rappepi/ESP32-S3-keyboard/hardware/Clavier.kicad_sch

## KiCad design hardware/Clavier.kicad_sch (2025-09-21)

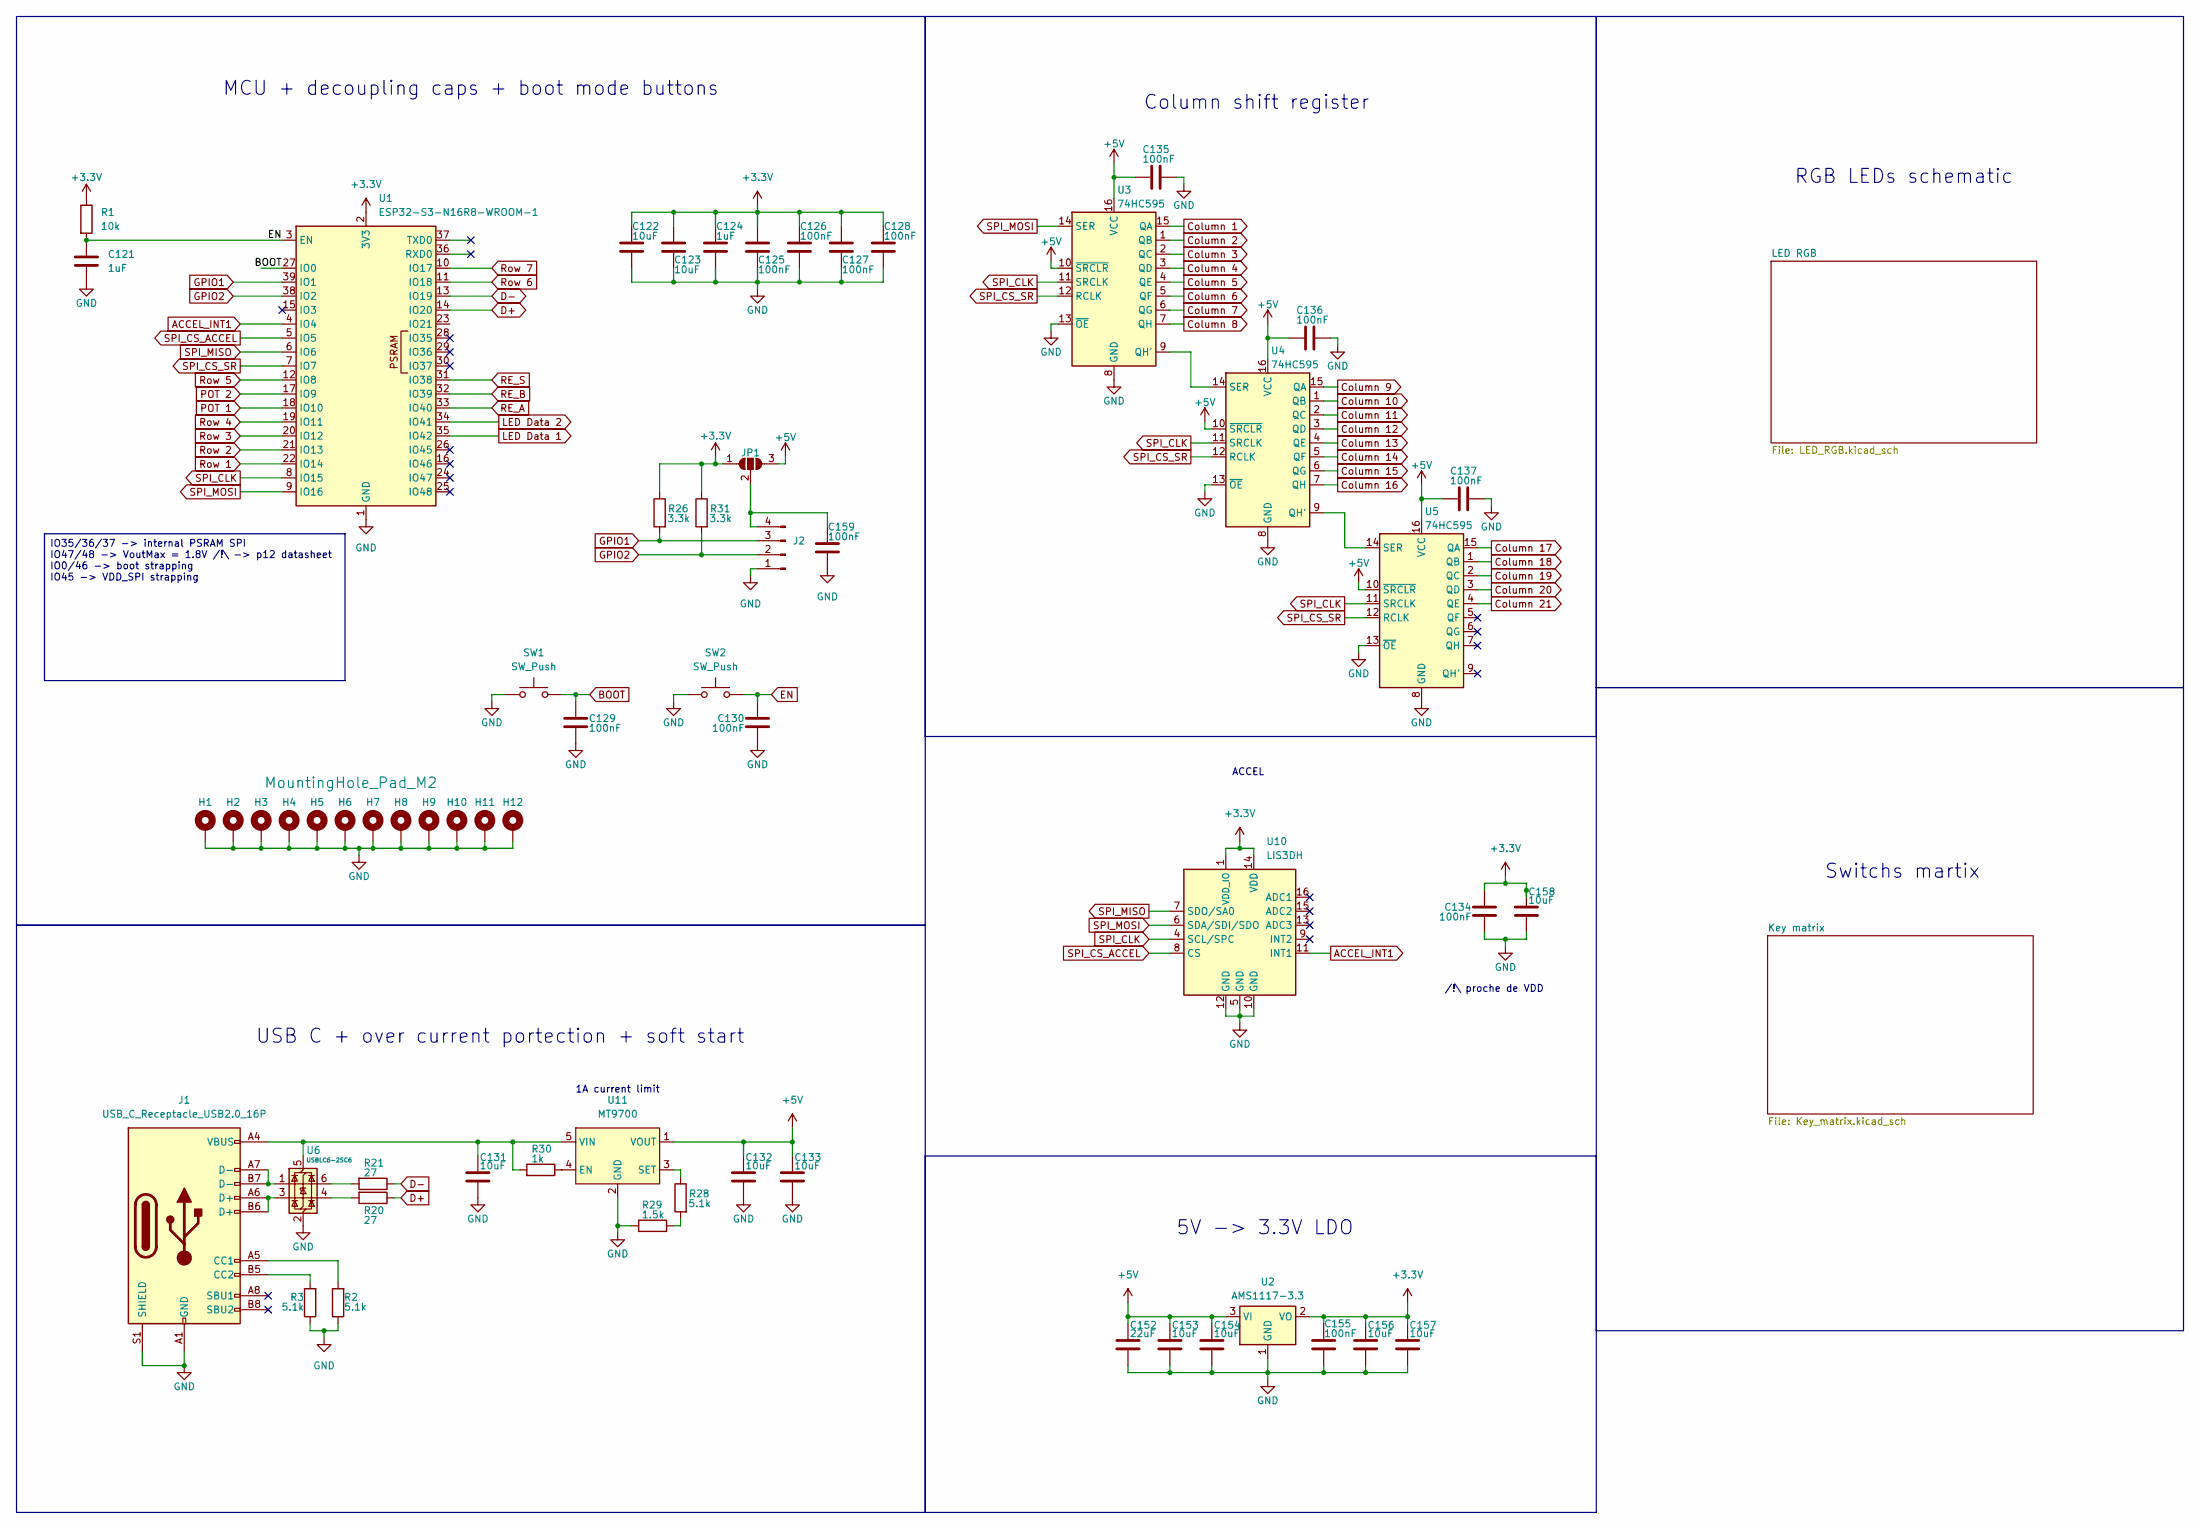
[picture p8: schematic Clavier.kicad_sch]

Parts:
C121, C124: 1uF; C_0402_1005Metric_Pad0.74x0.62mm_HandSolder
C122, C123: 10uF; C_0402_1005Metric_Pad0.74x0.62mm_HandSolder
C125, C126, C127, C128, C129, C130, C134, C135, C136, C137, C155, C159: 100nF; C_0402_1005Metric_Pad0.74x0.62mm_HandSolder
C131, C132, C133, C153, C154, C156, C157, C158: 10uF; C_0603_1608Metric_Pad1.08x0.95mm_HandSolder
C152: 22uF; C_1206_3216Metric_Pad1.33x1.80mm_HandSolder
H1, H2, H3, H4, H5, H6, H7, H8, H9, H10, H11, H12: MountingHole_Pad_M2; MountingHole_2.2mm_M2_ISO7380_Pad
J1: USB_C_Receptacle_USB2.0_16P; USB_C_Receptacle_G-Switch_GT-USB-7010ASV
J2: Conn_01x04_Pin; PinHeader_1x04_P2.54mm_Vertical
JP1: SolderJumper_3_Open; SolderJumper-3_P1.3mm_Open_Pad1.0x1.5mm_NumberLabels
R1: 10k; R_0402_1005Metric_Pad0.72x0.64mm_HandSolder
R2, R3, R28: 5.1k; R_0603_1608Metric_Pad0.98x0.95mm_HandSolder
R20, R21: 27; R_0603_1608Metric_Pad0.98x0.95mm_HandSolder
R26, R31: 3.3k; R_0603_1608Metric_Pad0.98x0.95mm_HandSolder
R29: 1.5k; R_0603_1608Metric_Pad0.98x0.95mm_HandSolder
R30: 1k; R_0603_1608Metric_Pad0.98x0.95mm_HandSolder
SW1, SW2: SW_Push; SW_SPST_SKQG_WithoutStem
U1: ESP32-S3-N16R8-WROOM-1; ESP32-S3-WROOM-1
U2: AMS1117-3.3; SOT-223-3_TabPin2
U3, U4, U5: 74HC595; SOP-16_3.9x9.9mm_P1.27mm
U6: USBLC6-2SC6; SOT-23-6
U10: LIS3DH; LGA-16_3x3mm_P0.5mm_LayoutBorder3x5y
U11: MT9700; SOT-23-5_L3.0-W1.7-P0.95-LS2.8-BR; LCSC Part C89855

Connections:
+3.3V: C122.1, C123.1, C124.1, C125.1, C126.1, C127.1, C128.1, C134.1, C155.1, C156.1, C157.1, C158.1, JP1.1 (A), R1.1, R26.1, R31.1, U1.2 (3V3), U2.2 (VO), U10.1 (VDD_IO), U10.14 (VDD)
+5V: C132.1, C133.1, C135.2, C136.2, C137.2, C152.1, C153.1, C154.1, JP1.3 (B), U2.3 (VI), U3.10 (~SRCLR), U3.16 (VCC), U4.10 (~SRCLR), U4.16 (VCC), U5.10 (~SRCLR), U5.16 (VCC), U11.1 (VOUT)
ACCEL_INT1: U1.4 (IO4), U10.11 (INT1)
BOOT: C129.1, SW1.2, U1.27 (IO0)
Column 1: U3.15 (QA)
Column 2: U3.1 (QB)
Column 3: U3.2 (QC)
Column 4: U3.3 (QD)
Column 5: U3.4 (QE)
Column 6: U3.5 (QF)
Column 7: U3.6 (QG)
Column 8: U3.7 (QH)
Column 9: U4.15 (QA)
Column 10: U4.1 (QB)
Column 11: U4.2 (QC)
Column 12: U4.3 (QD)
Column 13: U4.4 (QE)
Column 14: U4.5 (QF)
Column 15: U4.6 (QG)
Column 16: U4.7 (QH)
Column 17: U5.15 (QA)
Column 18: U5.1 (QB)
Column 19: U5.2 (QC)
Column 20: U5.3 (QD)
Column 21: U5.4 (QE)
D+: R20.1, U1.14 (IO20)
D-: R21.1, U1.13 (IO19)
EN: C121.1, C130.1, R1.2, SW2.2, U1.3 (EN)
GND: C121.2, C122.2, C123.2, C124.2, C125.2, C126.2, C127.2, C128.2, C129.2, C130.2, C131.2, C132.2, C133.2, C134.2, C135.1, C136.1, C137.1, C152.2, C153.2, C154.2, C155.2, C156.2, C157.2, C158.2, C159.2, H1.1, H2.1, H3.1, H4.1, H5.1, H6.1, H7.1, H8.1, H9.1, H10.1, H11.1, H12.1, J1.A1 (GND), J1.A12 (GND), J1.B1 (GND), J1.B12 (GND), J1.S1 (SHIELD), J2.1, R2.1, R3.1, R29.2, SW1.1, SW2.1, U1.1 (GND), U1.40 (GND), U1.41 (GND), U2.1 (GND), U3.8 (GND), U3.13 (~OE), U4.8 (GND), U4.13 (~OE), U5.8 (GND), U5.13 (~OE), U6.2 (GND), U10.5 (GND), U10.10 (GND), U10.12 (GND), U11.2 (GND)
GPIO1: J2.3, R26.2, U1.39 (IO1)
GPIO2: J2.2, R31.2, U1.38 (IO2)
LED Data 1: U1.35 (IO42)
LED Data 2: U1.34 (IO41)
unnamed: C131.1, J1.A4 (VBUS), J1.A9 (VBUS), J1.B4 (VBUS), J1.B9 (VBUS), R30.2, U6.5 (VBUS), U11.5 (VIN)
unnamed: C159.1, J2.4, JP1.2 (C)
unnamed: J1.A5 (CC1), R2.2
unnamed: J1.A6 (D+), J1.B6 (D+), U6.3 (I/O2)
unnamed: J1.A7 (D-), J1.B7 (D-), U6.1 (I/O1)
unnamed: J1.B5 (CC2), R3.2
unnamed: R20.2, U6.4 (I/O2)
unnamed: R21.2, U6.6 (I/O1)
unnamed: R28.1, U11.3 (SET)
unnamed: R28.2, R29.1
unnamed: R30.1, U11.4 (EN)
unnamed: U3.9 (QH'), U4.14 (SER)
unnamed: U4.9 (QH'), U5.14 (SER)
POT 1: U1.18 (IO10)
POT 2: U1.17 (IO9)
RE_A: U1.33 (IO40)
RE_B: U1.32 (IO39)
RE_S: U1.31 (IO38)
Row 1: U1.22 (IO14)
Row 2: U1.21 (IO13)
Row 3: U1.20 (IO12)
Row 4: U1.19 (IO11)
Row 5: U1.12 (IO8)
Row 6: U1.11 (IO18)
Row 7: U1.10 (IO17)
SPI_CLK: U1.8 (IO15), U3.11 (SRCLK), U4.11 (SRCLK), U5.11 (SRCLK), U10.4 (SCL/SPC)
SPI_CS_ACCEL: U1.5 (IO5), U10.8 (CS)
SPI_CS_SR: U1.7 (IO7), U3.12 (RCLK), U4.12 (RCLK), U5.12 (RCLK)
SPI_MISO: U1.6 (IO6), U10.7 (SDO/SA0)
SPI_MOSI: U1.9 (IO16), U3.14 (SER), U10.6 (SDA/SDI/SDO)

Notes on the sheet:
Column shift register
USB C + over current portection + soft start
5V -> 3.3V LDO
MCU + decoupling caps + boot mode buttons
Switchs martix
1A current limit
ACCEL
/!\ proche de VDD
RGB LEDs schematic
IO35/36/37 -> internal PSRAM SPI IO47/48 -> VoutMax = 1.8V /!\ -> p12 datasheet IO0/46 -> boot strapping IO45 -> VDD_SPI strapping
