rappepi/ESP32-S3-keyboard/hardware/LED_RGB.kicad_sch

## KiCad design hardware/LED_RGB.kicad_sch (2025-09-21)

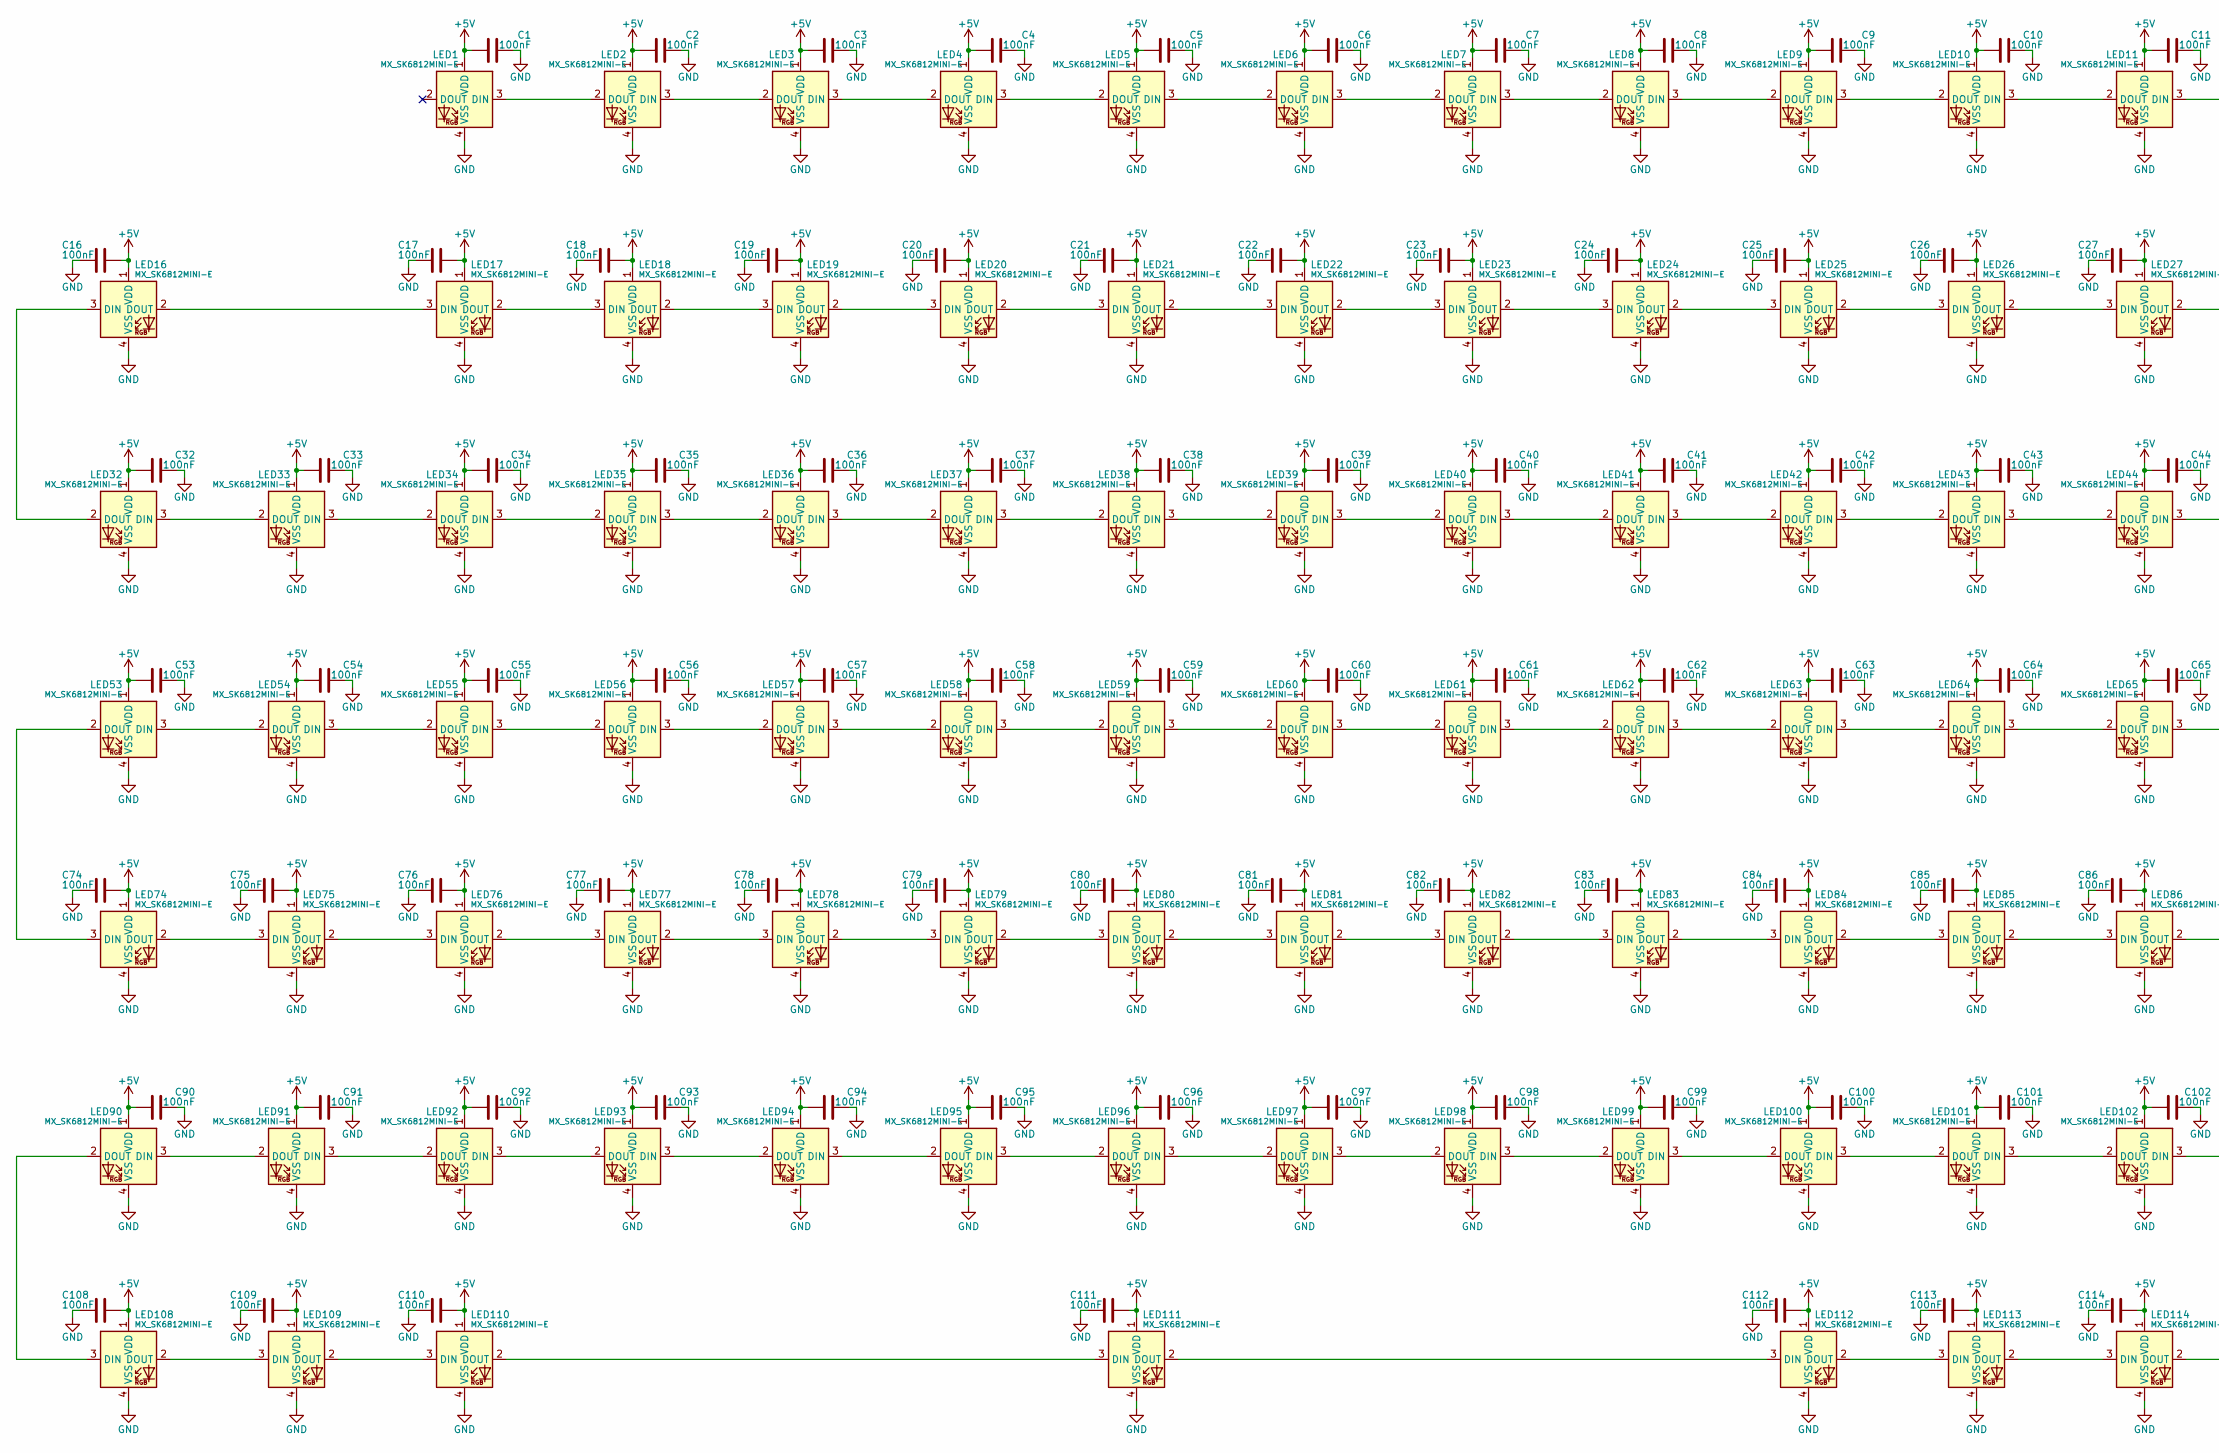
[picture p11: schematic LED_RGB.kicad_sch, part in row 1, column 1]

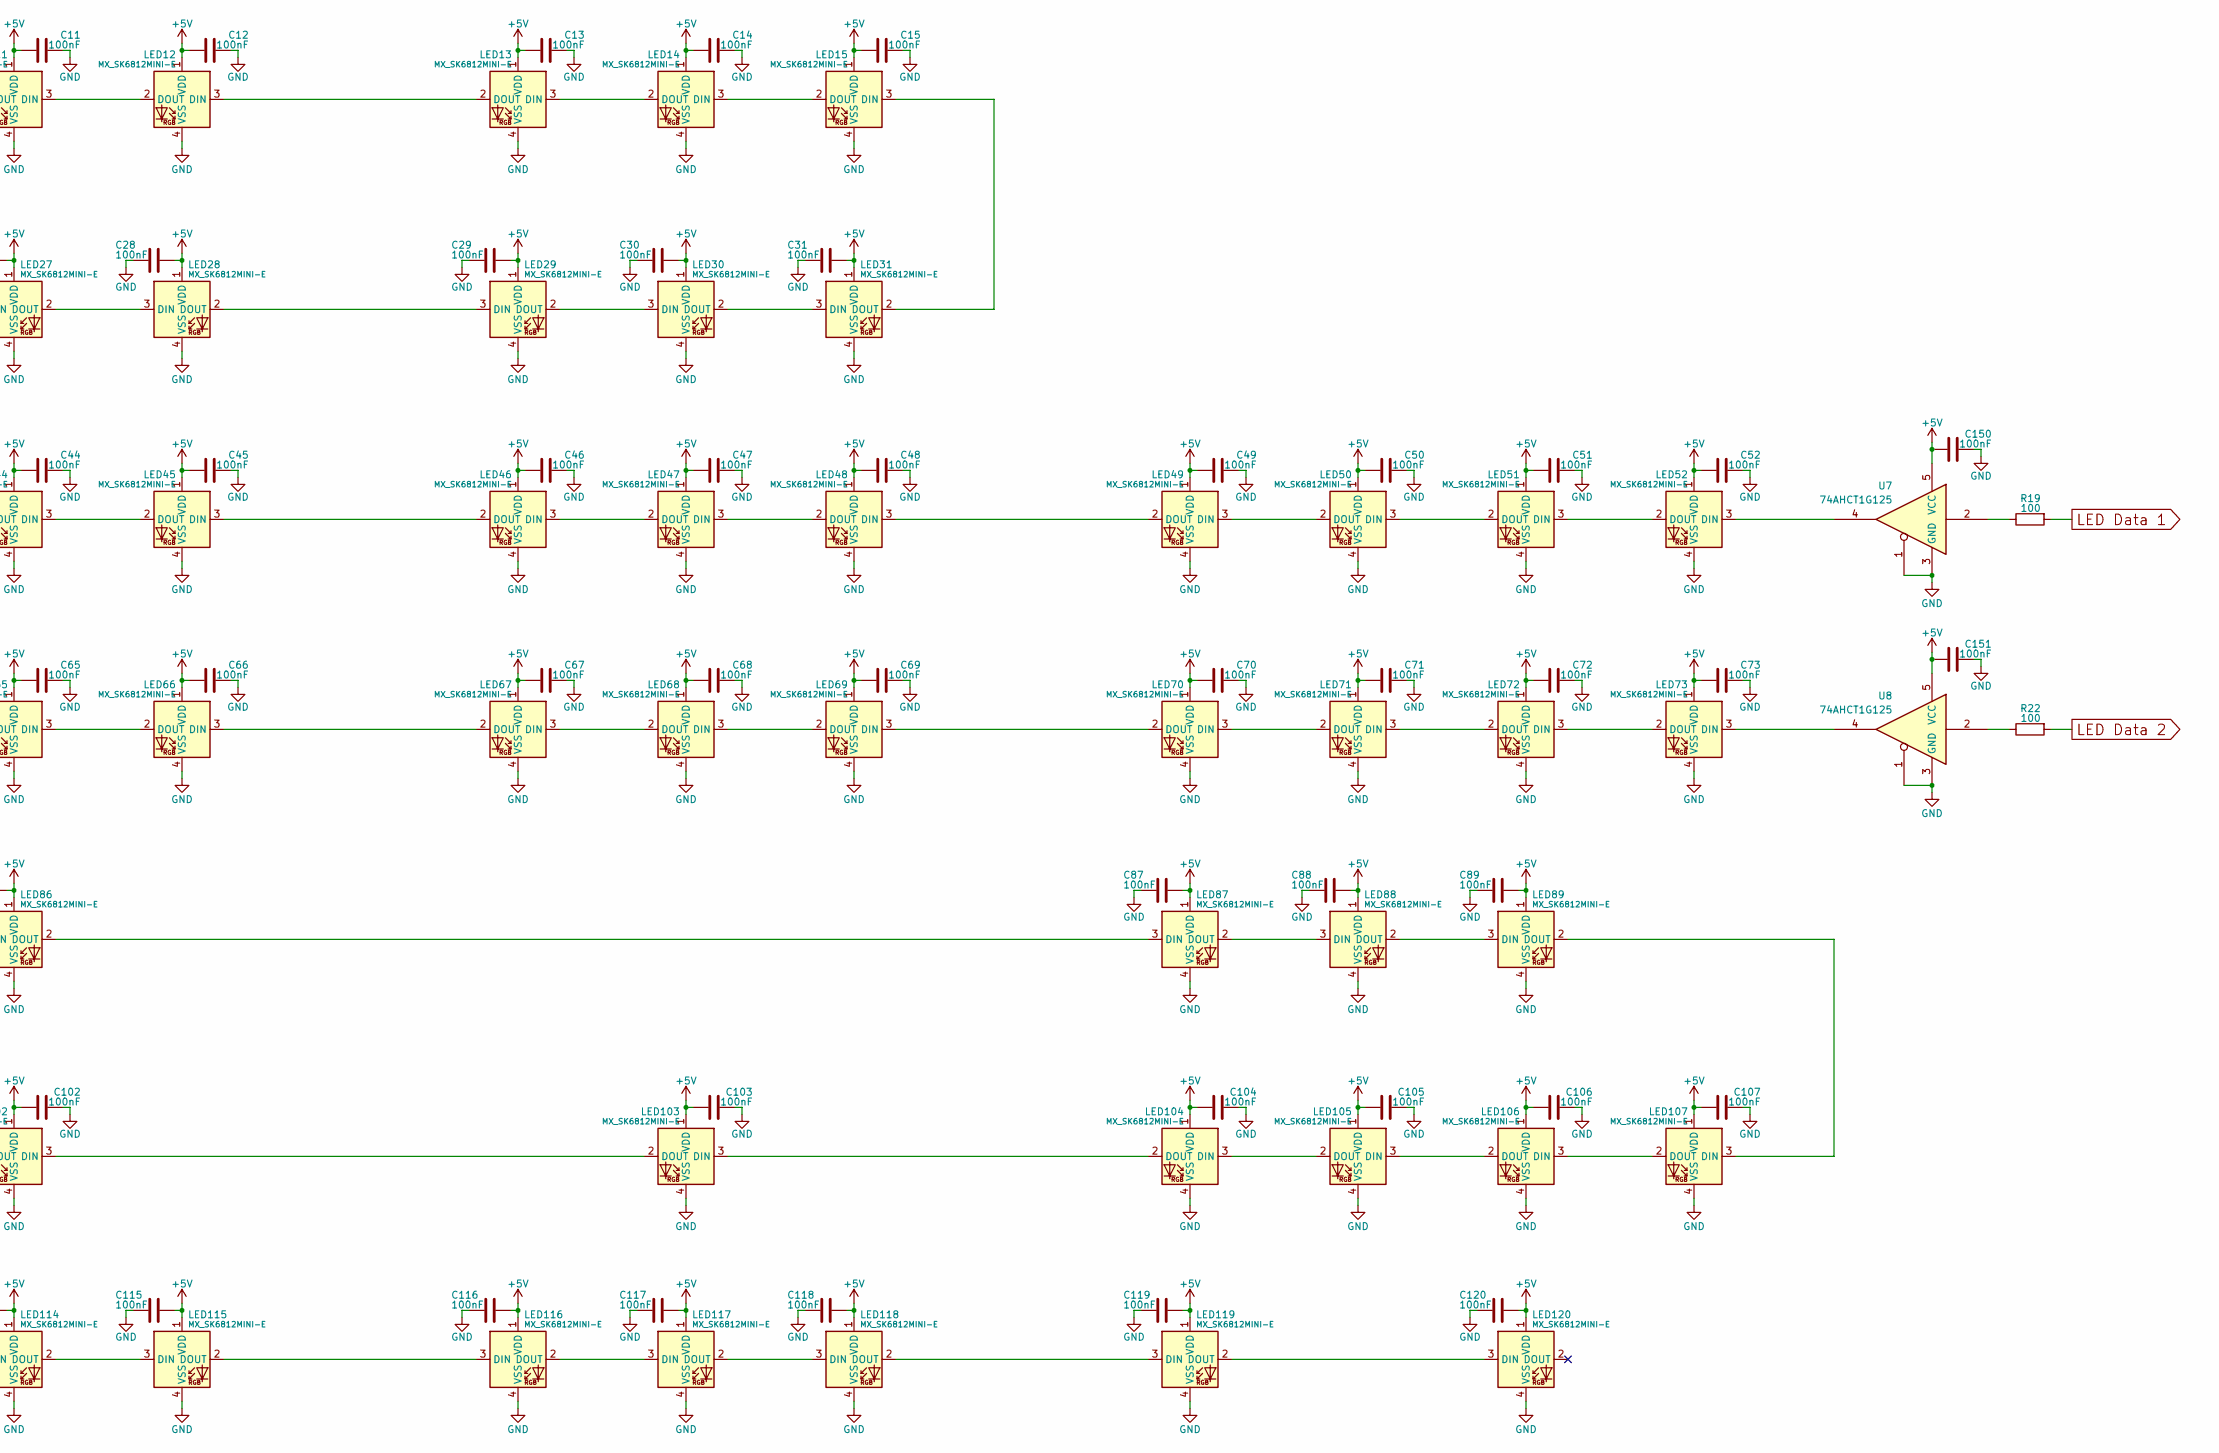
[picture p12: schematic LED_RGB.kicad_sch, part in row 1, column 2]

Parts:
C1, C2, C3, C4, C5, C6, C7, C8, C9, C10, C11, C12, C13, C14, C15, C16, C17, C18, C19, C20, C21, C22, C23, C24, C25, C26, C27, C28, C29, C30, C31, C32, C33, C34, C35, C36, C37, C38, C39, C40, C41, C42, C43, C44, C45, C46, C47, C48, C49, C50, C51, C52, C53, C54, C55, C56, C57, C58, C59, C60, C61, C62, C63, C64, C65, C66, C67, C68, C69, C70, C71, C72, C73, C74, C75, C76, C77, C78, C79, C80, C81, C82, C83, C84, C85, C86, C87, C88, C89, C90, C91, C92, C93, C94, C95, C96, C97, C98, C99, C100, C101, C102, C103, C104, C105, C106, C107, C108, C109, C110, C111, C112, C113, C114, C115, C116, C117, C118, C119, C120, C150, C151: 100nF; C_0402_1005Metric_Pad0.74x0.62mm_HandSolder
LED1, LED2, LED3, LED4, LED5, LED6, LED7, LED8, LED9, LED10, LED11, LED12, LED13, LED14, LED15, LED16, LED17, LED18, LED19, LED20, LED21, LED22, LED23, LED24, LED25, LED26, LED27, LED28, LED29, LED30, LED31, LED32, LED33, LED34, LED35, LED36, LED37, LED38, LED39, LED40, LED41, LED42, LED43, LED44, LED45, LED46, LED47, LED48, LED49, LED50, LED51, LED52, LED53, LED54, LED55, LED56, LED57, LED58, LED59, LED60, LED61, LED62, LED63, LED64, LED65, LED66, LED67, LED68, LED69, LED70, LED71, LED72, LED73, LED74, LED75, LED76, LED77, LED78, LED79, LED80, LED81, LED82, LED83, LED84, LED85, LED86, LED87, LED88, LED89, LED90, LED91, LED92, LED93, LED94, LED95, LED96, LED97, LED98, LED99, LED100, LED101, LED102, LED103, LED104, LED105, LED106, LED107, LED108, LED109, LED110, LED111, LED112, LED113, LED114, LED115, LED116, LED117, LED118, LED119, LED120: MX_SK6812MINI-E; LED_MX_6028R
R19, R22: 100; R_0603_1608Metric_Pad0.98x0.95mm_HandSolder
U7, U8: 74AHCT1G125; SOT-23-5_HandSoldering

Connections:
+5V: C1.2, C2.2, C3.2, C4.2, C5.2, C6.2, C7.2, C8.2, C9.2, C10.2, C11.2, C12.2, C13.2, C14.2, C15.2, C16.2, C17.2, C18.2, C19.2, C20.2, C21.2, C22.2, C23.2, C24.2, C25.2, C26.2, C27.2, C28.2, C29.2, C30.2, C31.2, C32.2, C33.2, C34.2, C35.2, C36.2, C37.2, C38.2, C39.2, C40.2, C41.2, C42.2, C43.2, C44.2, C45.2, C46.2, C47.2, C48.2, C49.2, C50.2, C51.2, C52.2, C53.2, C54.2, C55.2, C56.2, C57.2, C58.2, C59.2, C60.2, C61.2, C62.2, C63.2, C64.2, C65.2, C66.2, C67.2, C68.2, C69.2, C70.2, C71.2, C72.2, C73.2, C74.2, C75.2, C76.2, C77.2, C78.2, C79.2, C80.2, C81.2, C82.2, C83.2, C84.2, C85.2, C86.2, C87.2, C88.2, C89.2, C90.2, C91.2, C92.2, C93.2, C94.2, C95.2, C96.2, C97.2, C98.2, C99.2, C100.2, C101.2, C102.2, C103.2, C104.2, C105.2, C106.2, C107.2, C108.2, C109.2, C110.2, C111.2, C112.2, C113.2, C114.2, C115.2, C116.2, C117.2, C118.2, C119.2, C120.2, C150.2, C151.2, LED1.1 (VDD), LED2.1 (VDD), LED3.1 (VDD), LED4.1 (VDD), LED5.1 (VDD), LED6.1 (VDD), LED7.1 (VDD), LED8.1 (VDD), LED9.1 (VDD), LED10.1 (VDD), LED11.1 (VDD), LED12.1 (VDD), LED13.1 (VDD), LED14.1 (VDD), LED15.1 (VDD), LED16.1 (VDD), LED17.1 (VDD), LED18.1 (VDD), LED19.1 (VDD), LED20.1 (VDD), LED21.1 (VDD), LED22.1 (VDD), LED23.1 (VDD), LED24.1 (VDD), LED25.1 (VDD), LED26.1 (VDD), LED27.1 (VDD), LED28.1 (VDD), LED29.1 (VDD), LED30.1 (VDD), LED31.1 (VDD), LED32.1 (VDD), LED33.1 (VDD), LED34.1 (VDD), LED35.1 (VDD), LED36.1 (VDD), LED37.1 (VDD), LED38.1 (VDD), LED39.1 (VDD), LED40.1 (VDD), LED41.1 (VDD), LED42.1 (VDD), LED43.1 (VDD), LED44.1 (VDD), LED45.1 (VDD), LED46.1 (VDD), LED47.1 (VDD), LED48.1 (VDD), LED49.1 (VDD), LED50.1 (VDD), LED51.1 (VDD), LED52.1 (VDD), LED53.1 (VDD), LED54.1 (VDD), LED55.1 (VDD), LED56.1 (VDD), LED57.1 (VDD), LED58.1 (VDD), LED59.1 (VDD), LED60.1 (VDD), LED61.1 (VDD), LED62.1 (VDD), LED63.1 (VDD), LED64.1 (VDD), LED65.1 (VDD), LED66.1 (VDD), LED67.1 (VDD), LED68.1 (VDD), LED69.1 (VDD), LED70.1 (VDD), LED71.1 (VDD), LED72.1 (VDD), LED73.1 (VDD), LED74.1 (VDD), LED75.1 (VDD), LED76.1 (VDD), LED77.1 (VDD), LED78.1 (VDD), LED79.1 (VDD), LED80.1 (VDD), LED81.1 (VDD), LED82.1 (VDD), LED83.1 (VDD), LED84.1 (VDD), LED85.1 (VDD), LED86.1 (VDD), LED87.1 (VDD), LED88.1 (VDD), LED89.1 (VDD), LED90.1 (VDD), LED91.1 (VDD), LED92.1 (VDD), LED93.1 (VDD), LED94.1 (VDD), LED95.1 (VDD), LED96.1 (VDD), LED97.1 (VDD), LED98.1 (VDD), LED99.1 (VDD), LED100.1 (VDD), LED101.1 (VDD), LED102.1 (VDD), LED103.1 (VDD), LED104.1 (VDD), LED105.1 (VDD), LED106.1 (VDD), LED107.1 (VDD), LED108.1 (VDD), LED109.1 (VDD), LED110.1 (VDD), LED111.1 (VDD), LED112.1 (VDD), LED113.1 (VDD), LED114.1 (VDD), LED115.1 (VDD), LED116.1 (VDD), LED117.1 (VDD), LED118.1 (VDD), LED119.1 (VDD), LED120.1 (VDD), U7.5 (VCC), U8.5 (VCC)
GND: C1.1, C2.1, C3.1, C4.1, C5.1, C6.1, C7.1, C8.1, C9.1, C10.1, C11.1, C12.1, C13.1, C14.1, C15.1, C16.1, C17.1, C18.1, C19.1, C20.1, C21.1, C22.1, C23.1, C24.1, C25.1, C26.1, C27.1, C28.1, C29.1, C30.1, C31.1, C32.1, C33.1, C34.1, C35.1, C36.1, C37.1, C38.1, C39.1, C40.1, C41.1, C42.1, C43.1, C44.1, C45.1, C46.1, C47.1, C48.1, C49.1, C50.1, C51.1, C52.1, C53.1, C54.1, C55.1, C56.1, C57.1, C58.1, C59.1, C60.1, C61.1, C62.1, C63.1, C64.1, C65.1, C66.1, C67.1, C68.1, C69.1, C70.1, C71.1, C72.1, C73.1, C74.1, C75.1, C76.1, C77.1, C78.1, C79.1, C80.1, C81.1, C82.1, C83.1, C84.1, C85.1, C86.1, C87.1, C88.1, C89.1, C90.1, C91.1, C92.1, C93.1, C94.1, C95.1, C96.1, C97.1, C98.1, C99.1, C100.1, C101.1, C102.1, C103.1, C104.1, C105.1, C106.1, C107.1, C108.1, C109.1, C110.1, C111.1, C112.1, C113.1, C114.1, C115.1, C116.1, C117.1, C118.1, C119.1, C120.1, C150.1, C151.1, LED1.4 (VSS), LED2.4 (VSS), LED3.4 (VSS), LED4.4 (VSS), LED5.4 (VSS), LED6.4 (VSS), LED7.4 (VSS), LED8.4 (VSS), LED9.4 (VSS), LED10.4 (VSS), LED11.4 (VSS), LED12.4 (VSS), LED13.4 (VSS), LED14.4 (VSS), LED15.4 (VSS), LED16.4 (VSS), LED17.4 (VSS), LED18.4 (VSS), LED19.4 (VSS), LED20.4 (VSS), LED21.4 (VSS), LED22.4 (VSS), LED23.4 (VSS), LED24.4 (VSS), LED25.4 (VSS), LED26.4 (VSS), LED27.4 (VSS), LED28.4 (VSS), LED29.4 (VSS), LED30.4 (VSS), LED31.4 (VSS), LED32.4 (VSS), LED33.4 (VSS), LED34.4 (VSS), LED35.4 (VSS), LED36.4 (VSS), LED37.4 (VSS), LED38.4 (VSS), LED39.4 (VSS), LED40.4 (VSS), LED41.4 (VSS), LED42.4 (VSS), LED43.4 (VSS), LED44.4 (VSS), LED45.4 (VSS), LED46.4 (VSS), LED47.4 (VSS), LED48.4 (VSS), LED49.4 (VSS), LED50.4 (VSS), LED51.4 (VSS), LED52.4 (VSS), LED53.4 (VSS), LED54.4 (VSS), LED55.4 (VSS), LED56.4 (VSS), LED57.4 (VSS), LED58.4 (VSS), LED59.4 (VSS), LED60.4 (VSS), LED61.4 (VSS), LED62.4 (VSS), LED63.4 (VSS), LED64.4 (VSS), LED65.4 (VSS), LED66.4 (VSS), LED67.4 (VSS), LED68.4 (VSS), LED69.4 (VSS), LED70.4 (VSS), LED71.4 (VSS), LED72.4 (VSS), LED73.4 (VSS), LED74.4 (VSS), LED75.4 (VSS), LED76.4 (VSS), LED77.4 (VSS), LED78.4 (VSS), LED79.4 (VSS), LED80.4 (VSS), LED81.4 (VSS), LED82.4 (VSS), LED83.4 (VSS), LED84.4 (VSS), LED85.4 (VSS), LED86.4 (VSS), LED87.4 (VSS), LED88.4 (VSS), LED89.4 (VSS), LED90.4 (VSS), LED91.4 (VSS), LED92.4 (VSS), LED93.4 (VSS), LED94.4 (VSS), LED95.4 (VSS), LED96.4 (VSS), LED97.4 (VSS), LED98.4 (VSS), LED99.4 (VSS), LED100.4 (VSS), LED101.4 (VSS), LED102.4 (VSS), LED103.4 (VSS), LED104.4 (VSS), LED105.4 (VSS), LED106.4 (VSS), LED107.4 (VSS), LED108.4 (VSS), LED109.4 (VSS), LED110.4 (VSS), LED111.4 (VSS), LED112.4 (VSS), LED113.4 (VSS), LED114.4 (VSS), LED115.4 (VSS), LED116.4 (VSS), LED117.4 (VSS), LED118.4 (VSS), LED119.4 (VSS), LED120.4 (VSS), U7.1, U7.3 (GND), U8.1, U8.3 (GND)
LED Data 1: R19.2
LED Data 2: R22.2
unnamed: LED1.3 (DIN), LED2.2 (DOUT)
unnamed: LED2.3 (DIN), LED3.2 (DOUT)
unnamed: LED3.3 (DIN), LED4.2 (DOUT)
unnamed: LED4.3 (DIN), LED5.2 (DOUT)
unnamed: LED5.3 (DIN), LED6.2 (DOUT)
unnamed: LED6.3 (DIN), LED7.2 (DOUT)
unnamed: LED7.3 (DIN), LED8.2 (DOUT)
unnamed: LED8.3 (DIN), LED9.2 (DOUT)
unnamed: LED9.3 (DIN), LED10.2 (DOUT)
unnamed: LED10.3 (DIN), LED11.2 (DOUT)
unnamed: LED11.3 (DIN), LED12.2 (DOUT)
unnamed: LED12.3 (DIN), LED13.2 (DOUT)
unnamed: LED13.3 (DIN), LED14.2 (DOUT)
unnamed: LED14.3 (DIN), LED15.2 (DOUT)
unnamed: LED15.3 (DIN), LED31.2 (DOUT)
unnamed: LED16.2 (DOUT), LED17.3 (DIN)
unnamed: LED16.3 (DIN), LED32.2 (DOUT)
unnamed: LED17.2 (DOUT), LED18.3 (DIN)
unnamed: LED18.2 (DOUT), LED19.3 (DIN)
unnamed: LED19.2 (DOUT), LED20.3 (DIN)
unnamed: LED20.2 (DOUT), LED21.3 (DIN)
unnamed: LED21.2 (DOUT), LED22.3 (DIN)
unnamed: LED22.2 (DOUT), LED23.3 (DIN)
unnamed: LED23.2 (DOUT), LED24.3 (DIN)
unnamed: LED24.2 (DOUT), LED25.3 (DIN)
unnamed: LED25.2 (DOUT), LED26.3 (DIN)
unnamed: LED26.2 (DOUT), LED27.3 (DIN)
unnamed: LED27.2 (DOUT), LED28.3 (DIN)
unnamed: LED28.2 (DOUT), LED29.3 (DIN)
unnamed: LED29.2 (DOUT), LED30.3 (DIN)
unnamed: LED30.2 (DOUT), LED31.3 (DIN)
unnamed: LED32.3 (DIN), LED33.2 (DOUT)
unnamed: LED33.3 (DIN), LED34.2 (DOUT)
unnamed: LED34.3 (DIN), LED35.2 (DOUT)
unnamed: LED35.3 (DIN), LED36.2 (DOUT)
unnamed: LED36.3 (DIN), LED37.2 (DOUT)
unnamed: LED37.3 (DIN), LED38.2 (DOUT)
unnamed: LED38.3 (DIN), LED39.2 (DOUT)
unnamed: LED39.3 (DIN), LED40.2 (DOUT)
unnamed: LED40.3 (DIN), LED41.2 (DOUT)
unnamed: LED41.3 (DIN), LED42.2 (DOUT)
unnamed: LED42.3 (DIN), LED43.2 (DOUT)
unnamed: LED43.3 (DIN), LED44.2 (DOUT)
unnamed: LED44.3 (DIN), LED45.2 (DOUT)
unnamed: LED45.3 (DIN), LED46.2 (DOUT)
unnamed: LED46.3 (DIN), LED47.2 (DOUT)
unnamed: LED47.3 (DIN), LED48.2 (DOUT)
unnamed: LED48.3 (DIN), LED49.2 (DOUT)
unnamed: LED49.3 (DIN), LED50.2 (DOUT)
unnamed: LED50.3 (DIN), LED51.2 (DOUT)
unnamed: LED51.3 (DIN), LED52.2 (DOUT)
unnamed: LED52.3 (DIN), U7.4
unnamed: LED53.2 (DOUT), LED74.3 (DIN)
unnamed: LED53.3 (DIN), LED54.2 (DOUT)
unnamed: LED54.3 (DIN), LED55.2 (DOUT)
unnamed: LED55.3 (DIN), LED56.2 (DOUT)
unnamed: LED56.3 (DIN), LED57.2 (DOUT)
unnamed: LED57.3 (DIN), LED58.2 (DOUT)
unnamed: LED58.3 (DIN), LED59.2 (DOUT)
unnamed: LED59.3 (DIN), LED60.2 (DOUT)
unnamed: LED60.3 (DIN), LED61.2 (DOUT)
unnamed: LED61.3 (DIN), LED62.2 (DOUT)
unnamed: LED62.3 (DIN), LED63.2 (DOUT)
unnamed: LED63.3 (DIN), LED64.2 (DOUT)
unnamed: LED64.3 (DIN), LED65.2 (DOUT)
unnamed: LED65.3 (DIN), LED66.2 (DOUT)
unnamed: LED66.3 (DIN), LED67.2 (DOUT)
unnamed: LED67.3 (DIN), LED68.2 (DOUT)
unnamed: LED68.3 (DIN), LED69.2 (DOUT)
unnamed: LED69.3 (DIN), LED70.2 (DOUT)
unnamed: LED70.3 (DIN), LED71.2 (DOUT)
unnamed: LED71.3 (DIN), LED72.2 (DOUT)
unnamed: LED72.3 (DIN), LED73.2 (DOUT)
unnamed: LED73.3 (DIN), U8.4
unnamed: LED74.2 (DOUT), LED75.3 (DIN)
unnamed: LED75.2 (DOUT), LED76.3 (DIN)
unnamed: LED76.2 (DOUT), LED77.3 (DIN)
unnamed: LED77.2 (DOUT), LED78.3 (DIN)
unnamed: LED78.2 (DOUT), LED79.3 (DIN)
unnamed: LED79.2 (DOUT), LED80.3 (DIN)
unnamed: LED80.2 (DOUT), LED81.3 (DIN)
unnamed: LED81.2 (DOUT), LED82.3 (DIN)
unnamed: LED82.2 (DOUT), LED83.3 (DIN)
unnamed: LED83.2 (DOUT), LED84.3 (DIN)
unnamed: LED84.2 (DOUT), LED85.3 (DIN)
unnamed: LED85.2 (DOUT), LED86.3 (DIN)
unnamed: LED86.2 (DOUT), LED87.3 (DIN)
unnamed: LED87.2 (DOUT), LED88.3 (DIN)
unnamed: LED88.2 (DOUT), LED89.3 (DIN)
unnamed: LED90.3 (DIN), LED91.2 (DOUT)
unnamed: LED91.3 (DIN), LED92.2 (DOUT)
unnamed: LED92.3 (DIN), LED93.2 (DOUT)
unnamed: LED93.3 (DIN), LED94.2 (DOUT)
unnamed: LED94.3 (DIN), LED95.2 (DOUT)
unnamed: LED95.3 (DIN), LED96.2 (DOUT)
unnamed: LED96.3 (DIN), LED97.2 (DOUT)
unnamed: LED97.3 (DIN), LED98.2 (DOUT)
unnamed: LED98.3 (DIN), LED99.2 (DOUT)
unnamed: LED99.3 (DIN), LED100.2 (DOUT)
unnamed: LED100.3 (DIN), LED101.2 (DOUT)
unnamed: LED101.3 (DIN), LED102.2 (DOUT)
unnamed: LED102.3 (DIN), LED103.2 (DOUT)
unnamed: LED103.3 (DIN), LED104.2 (DOUT)
unnamed: LED104.3 (DIN), LED105.2 (DOUT)
unnamed: LED105.3 (DIN), LED106.2 (DOUT)
unnamed: LED106.3 (DIN), LED107.2 (DOUT)
unnamed: LED89.2 (DOUT), LED107.3 (DIN)
unnamed: LED108.2 (DOUT), LED109.3 (DIN)
unnamed: LED90.2 (DOUT), LED108.3 (DIN)
unnamed: LED109.2 (DOUT), LED110.3 (DIN)
unnamed: LED110.2 (DOUT), LED111.3 (DIN)
unnamed: LED111.2 (DOUT), LED112.3 (DIN)
unnamed: LED112.2 (DOUT), LED113.3 (DIN)
unnamed: LED113.2 (DOUT), LED114.3 (DIN)
unnamed: LED114.2 (DOUT), LED115.3 (DIN)
unnamed: LED115.2 (DOUT), LED116.3 (DIN)
unnamed: LED116.2 (DOUT), LED117.3 (DIN)
unnamed: LED117.2 (DOUT), LED118.3 (DIN)
unnamed: LED118.2 (DOUT), LED119.3 (DIN)
unnamed: LED119.2 (DOUT), LED120.3 (DIN)
unnamed: R19.1, U7.2
unnamed: R22.1, U8.2
